jtflanagan/AppleTini/v5/verilog/v5_1_2/v5_1_2.srcs/constrs_1/new/tini.xdc

set_property PACKAGE_PIN T15 [get_ports {apple_data_pin[0]}]
set_property IOSTANDARD LVCMOS33 [get_ports {apple_data_pin[0]}]
set_property PACKAGE_PIN N12 [get_ports {apple_data_pin[1]}]
set_property IOSTANDARD LVCMOS33 [get_ports {apple_data_pin[1]}]
set_property PACKAGE_PIN R16 [get_ports {apple_data_pin[2]}]
set_property IOSTANDARD LVCMOS33 [get_ports {apple_data_pin[2]}]
set_property PACKAGE_PIN P1 [get_ports {apple_data_pin[3]}]
set_property IOSTANDARD LVCMOS33 [get_ports {apple_data_pin[3]}]
set_property PACKAGE_PIN E1 [get_ports {apple_data_pin[4]}]
set_property IOSTANDARD LVCMOS33 [get_ports {apple_data_pin[4]}]
set_property PACKAGE_PIN H1 [get_ports {apple_data_pin[5]}]
set_property IOSTANDARD LVCMOS33 [get_ports {apple_data_pin[5]}]
set_property PACKAGE_PIN J1 [get_ports {apple_data_pin[6]}]
set_property IOSTANDARD LVCMOS33 [get_ports {apple_data_pin[6]}]
set_property PACKAGE_PIN N6 [get_ports {apple_data_pin[7]}]
set_property IOSTANDARD LVCMOS33 [get_ports {apple_data_pin[7]}]
set_property PACKAGE_PIN M6 [get_ports {apple_addr_pin[0]}]
set_property IOSTANDARD LVCMOS33 [get_ports {apple_addr_pin[0]}]
set_property PACKAGE_PIN K1 [get_ports {apple_addr_pin[1]}]
set_property IOSTANDARD LVCMOS33 [get_ports {apple_addr_pin[1]}]
set_property PACKAGE_PIN H2 [get_ports {apple_addr_pin[2]}]
set_property IOSTANDARD LVCMOS33 [get_ports {apple_addr_pin[2]}]
set_property PACKAGE_PIN F2 [get_ports {apple_addr_pin[3]}]
set_property IOSTANDARD LVCMOS33 [get_ports {apple_addr_pin[3]}]
set_property PACKAGE_PIN N9 [get_ports {apple_addr_pin[4]}]
set_property IOSTANDARD LVCMOS33 [get_ports {apple_addr_pin[4]}]
set_property PACKAGE_PIN P9 [get_ports {apple_addr_pin[5]}]
set_property IOSTANDARD LVCMOS33 [get_ports {apple_addr_pin[5]}]
set_property PACKAGE_PIN L3 [get_ports {apple_addr_pin[6]}]
set_property IOSTANDARD LVCMOS33 [get_ports {apple_addr_pin[6]}]
set_property PACKAGE_PIN L2 [get_ports {apple_addr_pin[7]}]
set_property IOSTANDARD LVCMOS33 [get_ports {apple_addr_pin[7]}]
set_property PACKAGE_PIN K3 [get_ports {apple_addr_pin[8]}]
set_property IOSTANDARD LVCMOS33 [get_ports {apple_addr_pin[8]}]
set_property PACKAGE_PIN K2 [get_ports {apple_addr_pin[9]}]
set_property IOSTANDARD LVCMOS33 [get_ports {apple_addr_pin[9]}]
set_property PACKAGE_PIN J3 [get_ports {apple_addr_pin[10]}]
set_property IOSTANDARD LVCMOS33 [get_ports {apple_addr_pin[10]}]
set_property PACKAGE_PIN H3 [get_ports {apple_addr_pin[11]}]
set_property IOSTANDARD LVCMOS33 [get_ports {apple_addr_pin[11]}]
set_property PACKAGE_PIN H5 [get_ports {apple_addr_pin[12]}]
set_property IOSTANDARD LVCMOS33 [get_ports {apple_addr_pin[12]}]
set_property PACKAGE_PIN H4 [get_ports {apple_addr_pin[13]}]
set_property IOSTANDARD LVCMOS33 [get_ports {apple_addr_pin[13]}]
set_property PACKAGE_PIN J5 [get_ports {apple_addr_pin[14]}]
set_property IOSTANDARD LVCMOS33 [get_ports {apple_addr_pin[14]}]
set_property PACKAGE_PIN J4 [get_ports {apple_addr_pin[15]}]
set_property IOSTANDARD LVCMOS33 [get_ports {apple_addr_pin[15]}]
set_property PACKAGE_PIN G5 [get_ports {apple_rw_pin}]
set_property IOSTANDARD LVCMOS33 [get_ports {apple_rw_pin}]
set_property PACKAGE_PIN C1 [get_ports {apple_phi0_pin}]
set_property IOSTANDARD LVCMOS33 [get_ports {apple_phi0_pin}]
set_property PACKAGE_PIN B1 [get_ports {apple_m2sel_pin}]
set_property IOSTANDARD LVCMOS33 [get_ports {apple_m2sel_pin}]
set_property PACKAGE_PIN B2 [get_ports {apple_q3_pin}]
set_property IOSTANDARD LVCMOS33 [get_ports {apple_q3_pin}]
set_property PACKAGE_PIN A2 [get_ports {apple_7m_pin}]
set_property IOSTANDARD LVCMOS33 [get_ports {apple_7m_pin}]
set_property PACKAGE_PIN D6 [get_ports {apple_m2b0_pin}]
set_property IOSTANDARD LVCMOS33 [get_ports {apple_m2b0_pin}]
set_property PACKAGE_PIN D1 [get_ports {apple_inh_pin}]
set_property IOSTANDARD LVCMOS33 [get_ports {apple_inh_pin}]
set_property PACKAGE_PIN A4 [get_ports {apple_res_pin}]
set_property IOSTANDARD LVCMOS33 [get_ports {apple_res_pin}]
set_property PACKAGE_PIN A5 [get_ports {apple_irq_pin}]
set_property IOSTANDARD LVCMOS33 [get_ports {apple_irq_pin}]
set_property PACKAGE_PIN K5 [get_ports {apple_rdy_pin}]
set_property IOSTANDARD LVCMOS33 [get_ports {apple_rdy_pin}]
set_property PACKAGE_PIN E6 [get_ports {apple_nmi_pin}]
set_property IOSTANDARD LVCMOS33 [get_ports {apple_nmi_pin}]
set_property PACKAGE_PIN G4 [get_ports {apple_dma_pin}]
set_property IOSTANDARD LVCMOS33 [get_ports {apple_dma_pin}]
set_property PACKAGE_PIN M2 [get_ports {tini_oe_pin}]
set_property IOSTANDARD LVCMOS33 [get_ports {tini_oe_pin}]
set_property PACKAGE_PIN M1 [get_ports {tini_oe_bar_pin}]
set_property IOSTANDARD LVCMOS33 [get_ports {tini_oe_bar_pin}]
set_property PACKAGE_PIN T13 [get_ports {tini_5v_pin}]
set_property IOSTANDARD LVCMOS33 [get_ports {tini_5v_pin}]
set_property PACKAGE_PIN R8 [get_ports {tini_addr_dir_pin}]
set_property IOSTANDARD LVCMOS33 [get_ports {tini_addr_dir_pin}]
set_property PACKAGE_PIN P8 [get_ports {tini_data_dir_pin}]
set_property IOSTANDARD LVCMOS33 [get_ports {tini_data_dir_pin}]


set_input_delay -clock [get_clocks clk_0] -min -add_delay 0.000 [get_ports apple_phi0_pin]
set_input_delay -clock [get_clocks clk_0] -max -add_delay 0.001 [get_ports apple_phi0_pin]
